CIJoris/PomoDesk/Graphics/axis.png

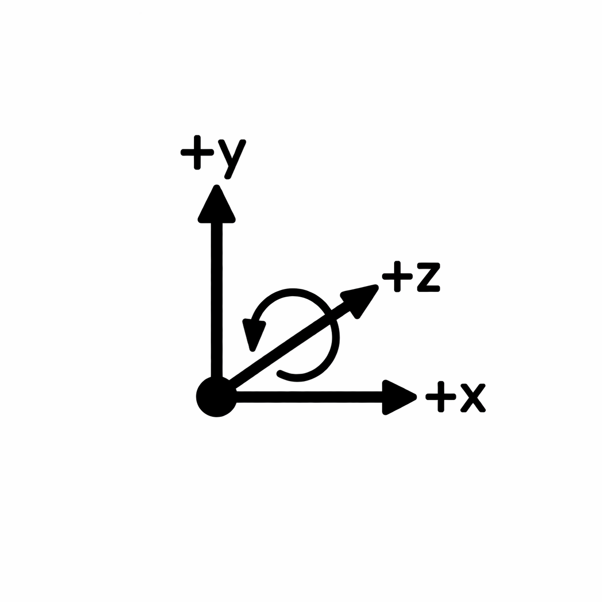
Graphics/axis.png
