CIJoris/PomoDesk/Graphics/pomo.png

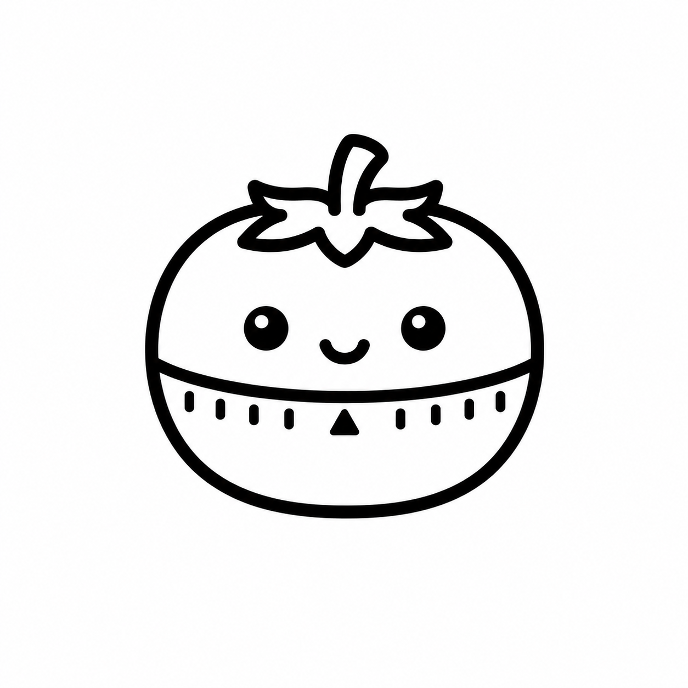
Graphics/pomo.png
