CIJoris/PomoDesk/Graphics/pomo_red.jpg

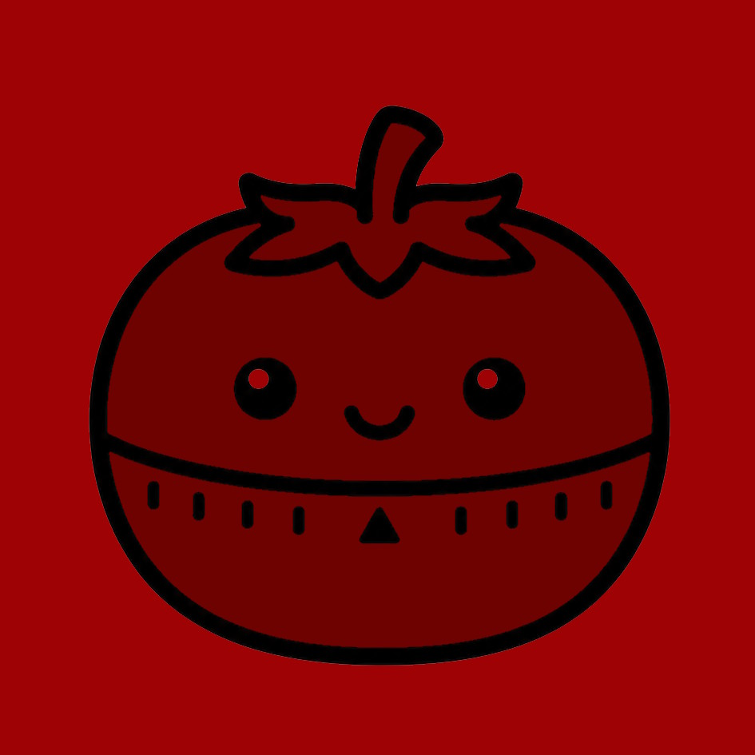
Graphics/pomo_red.jpg
