CIJoris/PomoDesk/Graphics/pomo_red_white.jpg

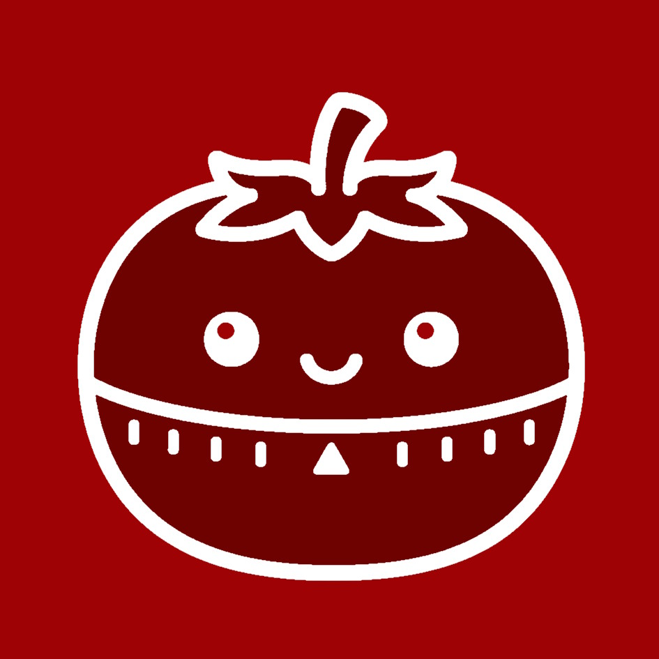
Graphics/pomo_red_white.jpg
