CIJoris/PomoDesk/Graphics/pomo_white_red.jpg

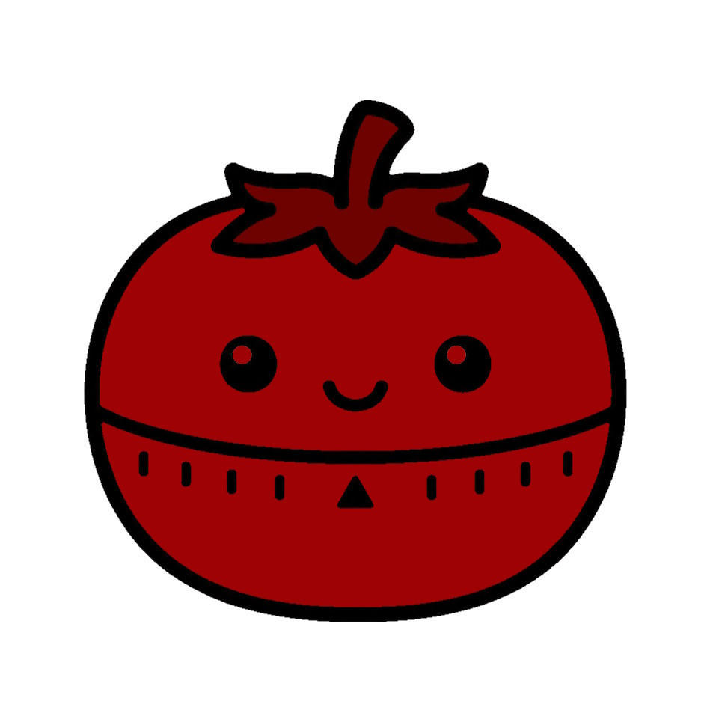
Graphics/pomo_white_red.jpg
