CIJoris/PomoDesk/Photos/pomo-desk-green.jpeg

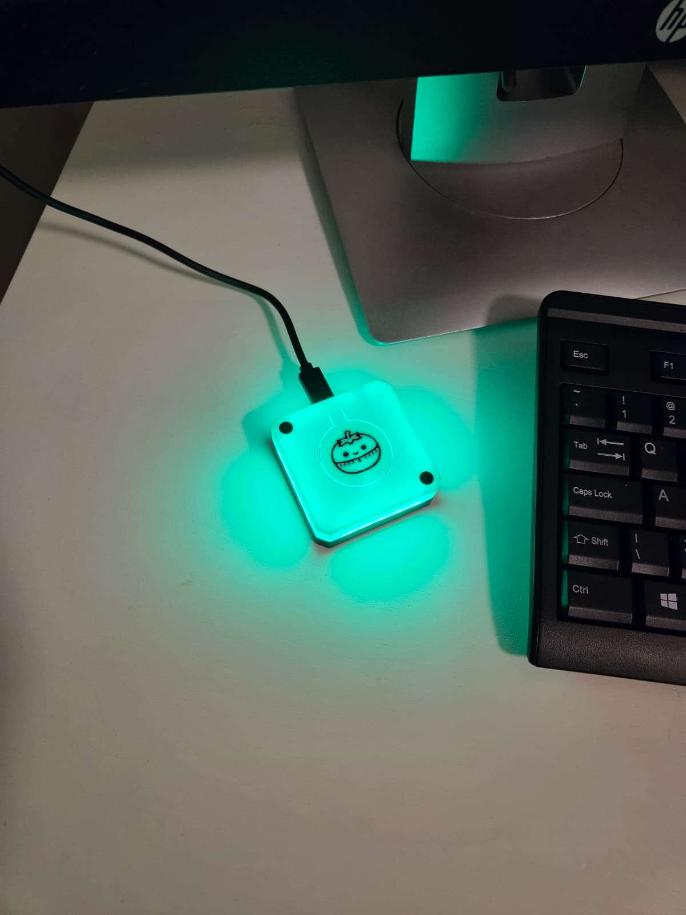
Photos/pomo-desk-green.jpeg
