CIJoris/PomoDesk/Photos/pomo-desk-orange.jpeg

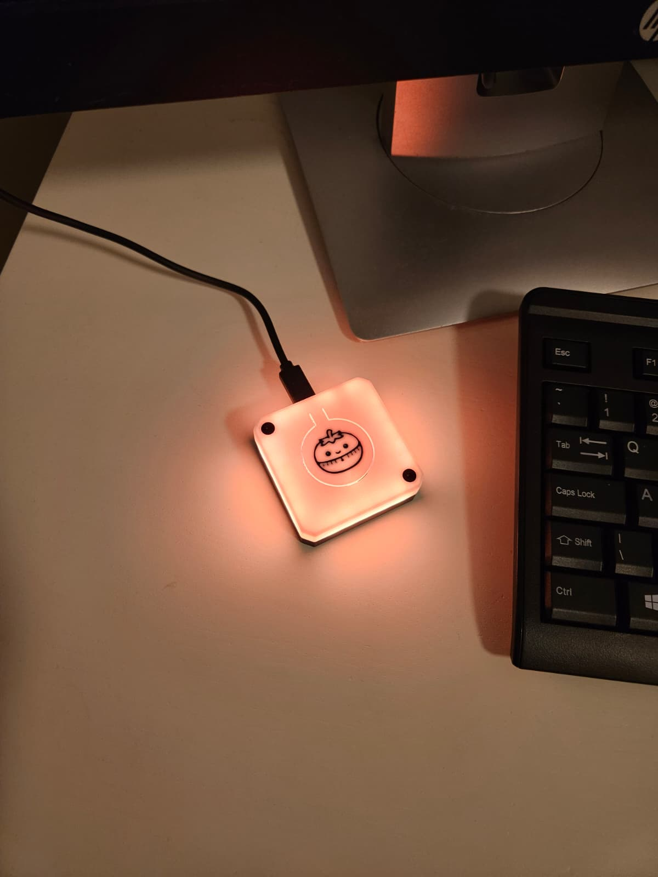
Photos/pomo-desk-orange.jpeg
