CIJoris/PomoDesk/Photos/pomo-desk-red.jpeg

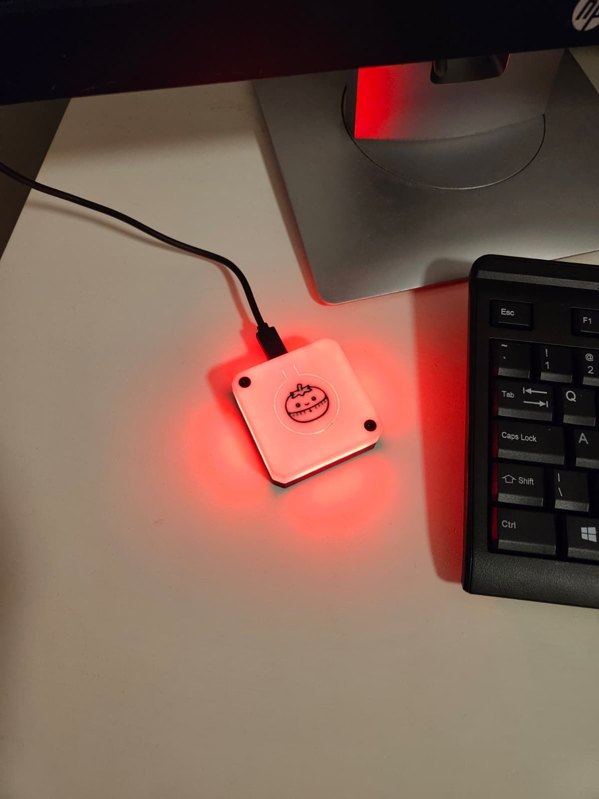
Photos/pomo-desk-red.jpeg
